S0550000000/github/doc/jawbreaker-fd0-145436.jpeg

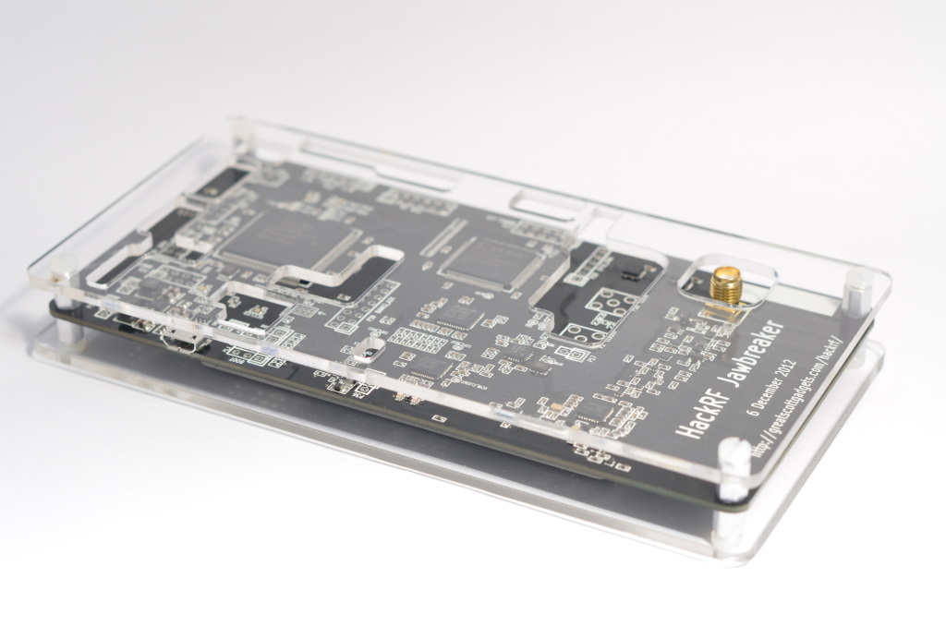
doc/jawbreaker-fd0-145436.jpeg
