S0550000000/github/doc/jawbreaker.jpeg

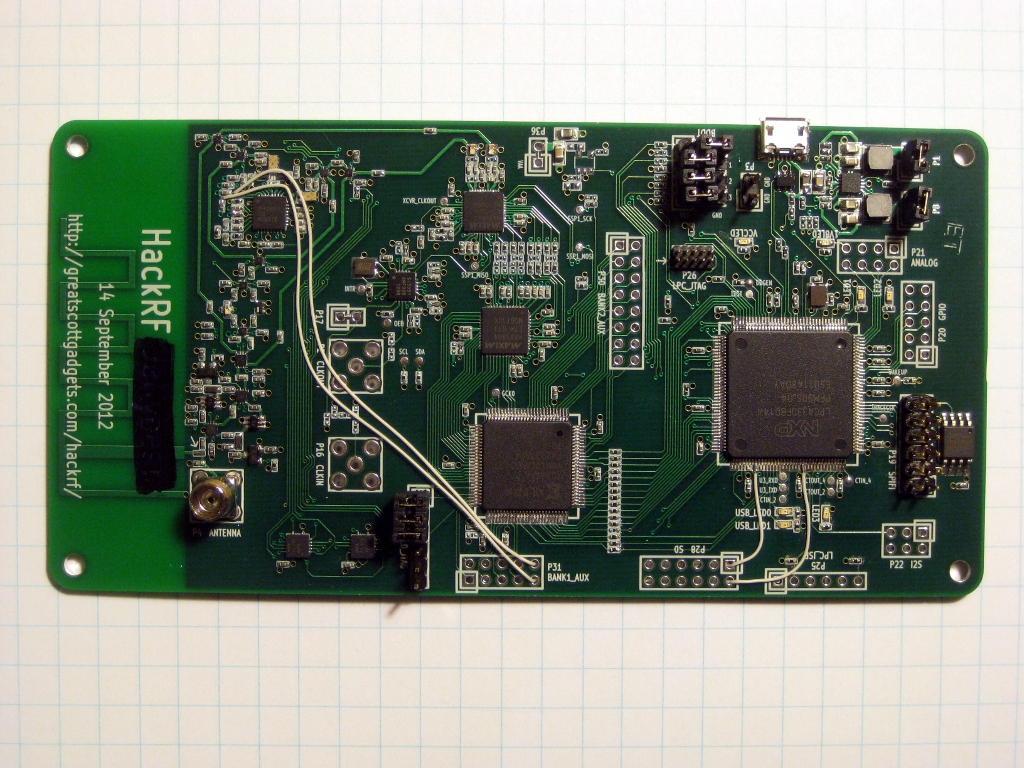
doc/jawbreaker.jpeg
