S0550000000/github/doc/lemonAndjelly.jpeg

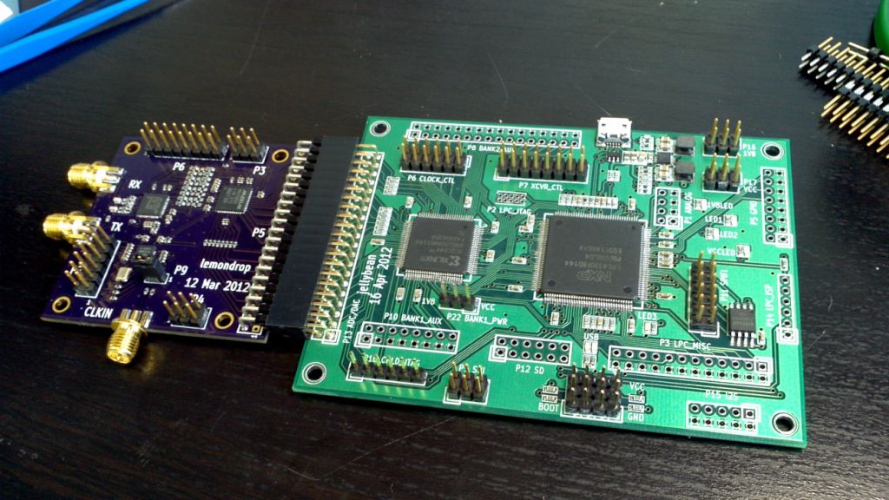
doc/lemonAndjelly.jpeg
