S0550000000/github/doc/wiki/images/hackrf_blockdiagram-digital.png

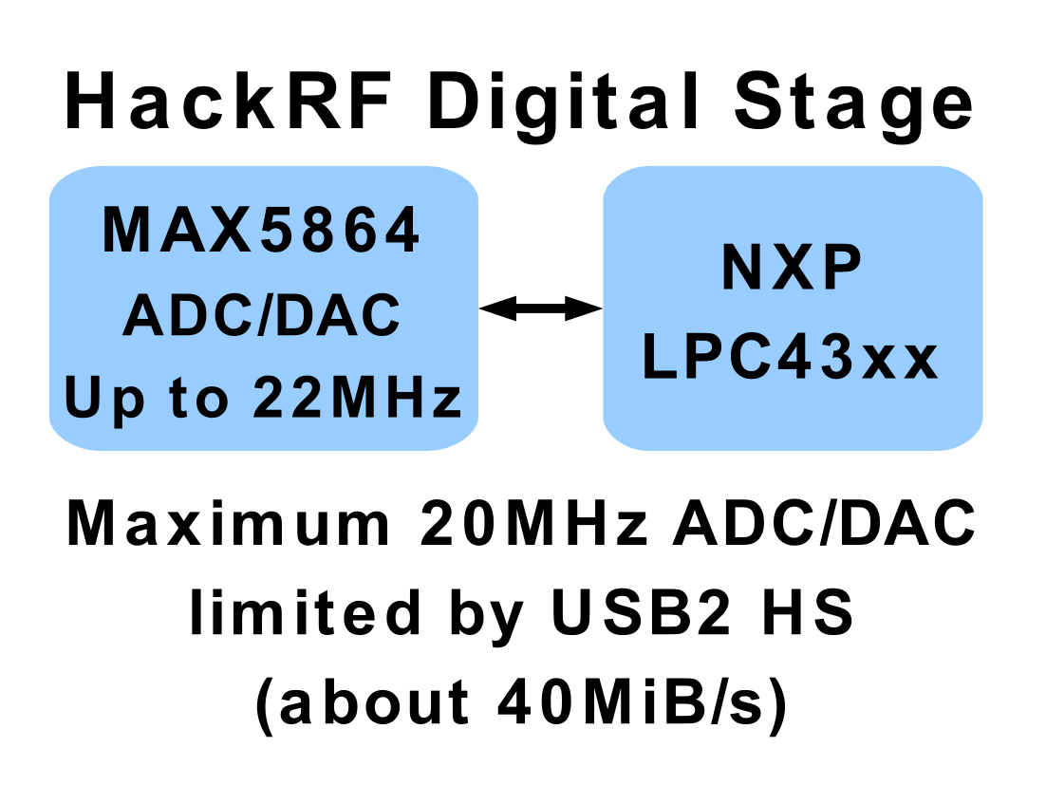
doc/wiki/images/hackrf_blockdiagram-digital.png
