S0550000000/github/doc/wiki/images/hackrf_blockdiagram-frontend_baseband.png

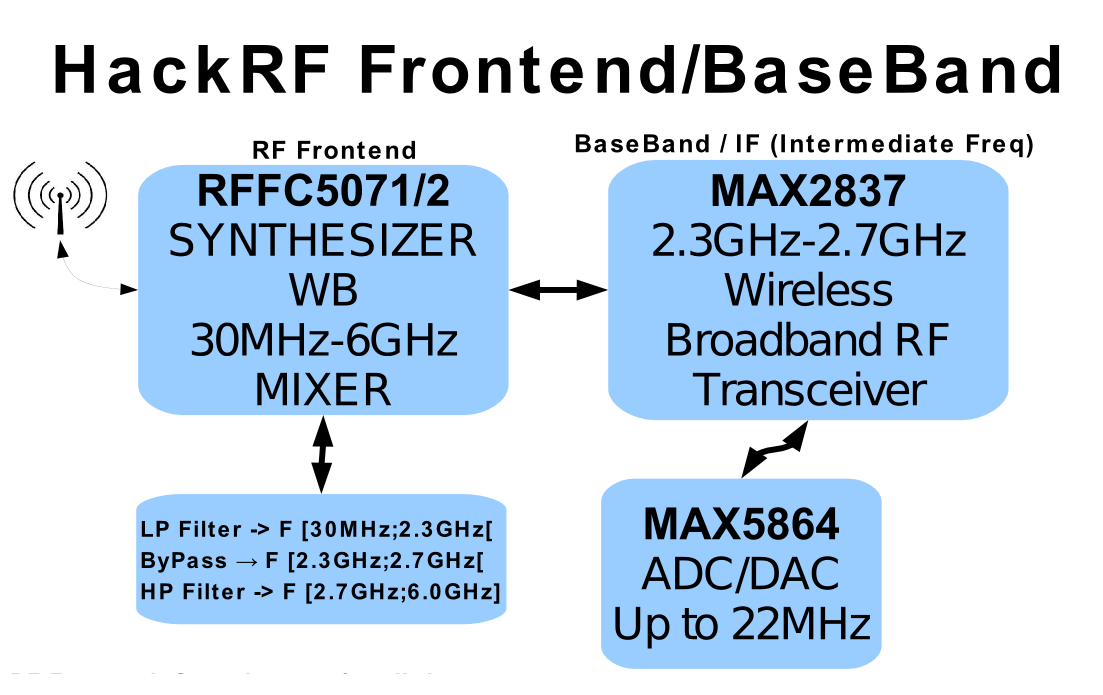
doc/wiki/images/hackrf_blockdiagram-frontend_baseband.png
