S0550000000/github/hardware/hackrf-one/PlasticCase_CAD/Case_With_HackRF.png

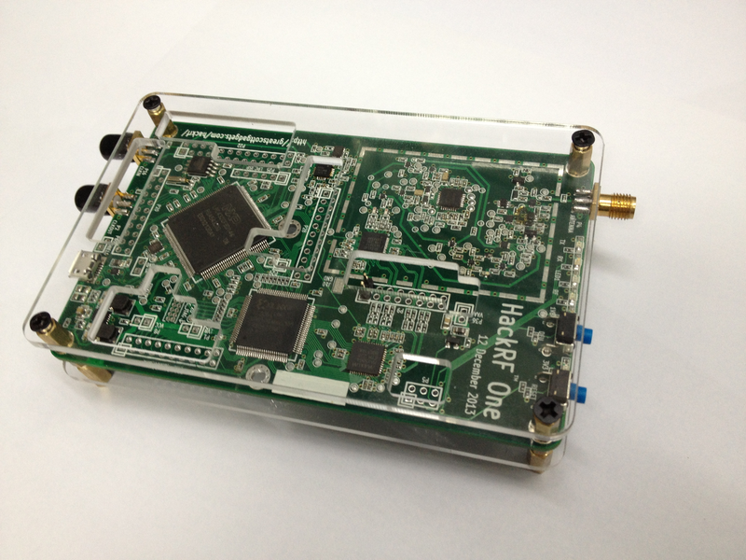
hardware/hackrf-one/PlasticCase_CAD/Case_With_HackRF.png
