S0550000000/github/hardware/hackrf-one/SoBv1_HackRF_One_16Janv2014/SoBv1_HackRF_One_Top2D.png

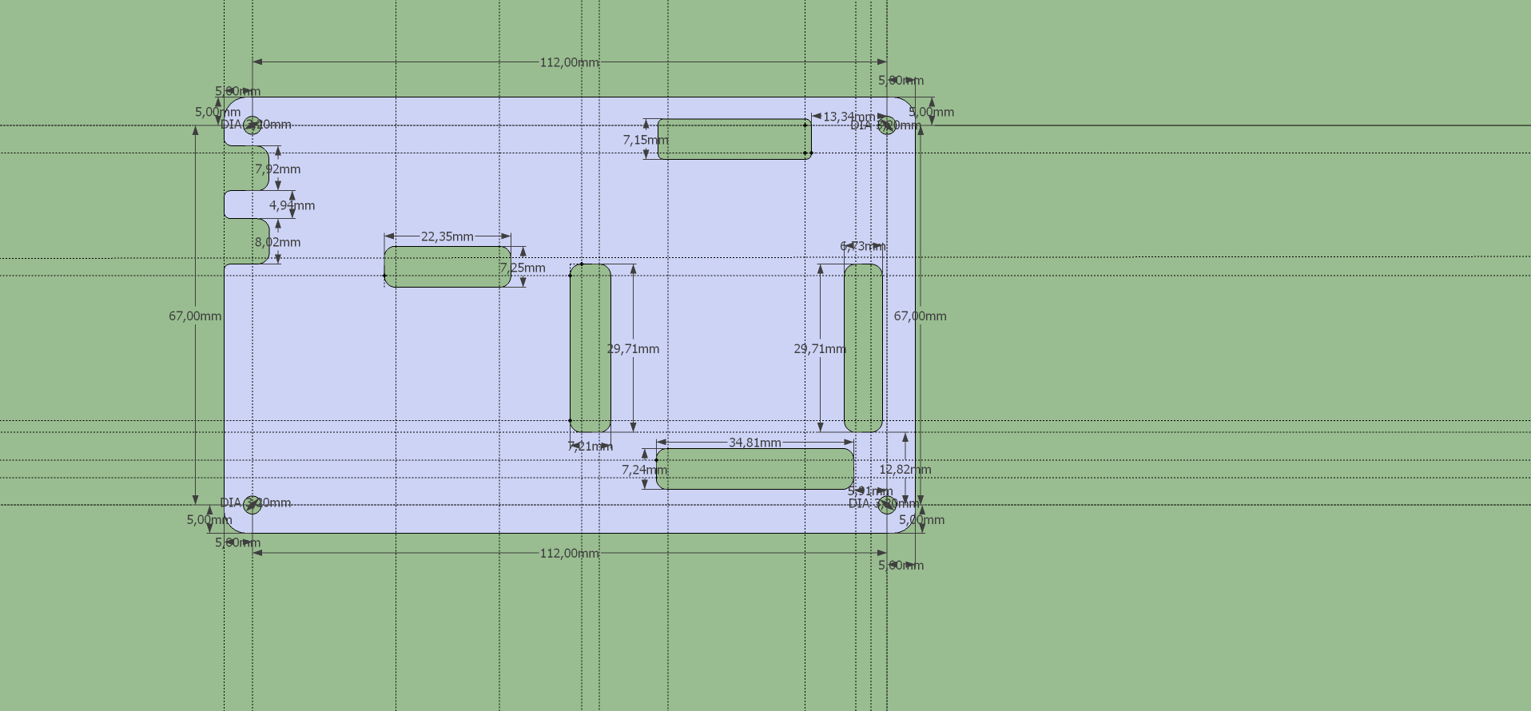
hardware/hackrf-one/SoBv1_HackRF_One_16Janv2014/SoBv1_HackRF_One_Top2D.png
