S0550000000/github/hardware/jellybean/JellyBean_pins.png

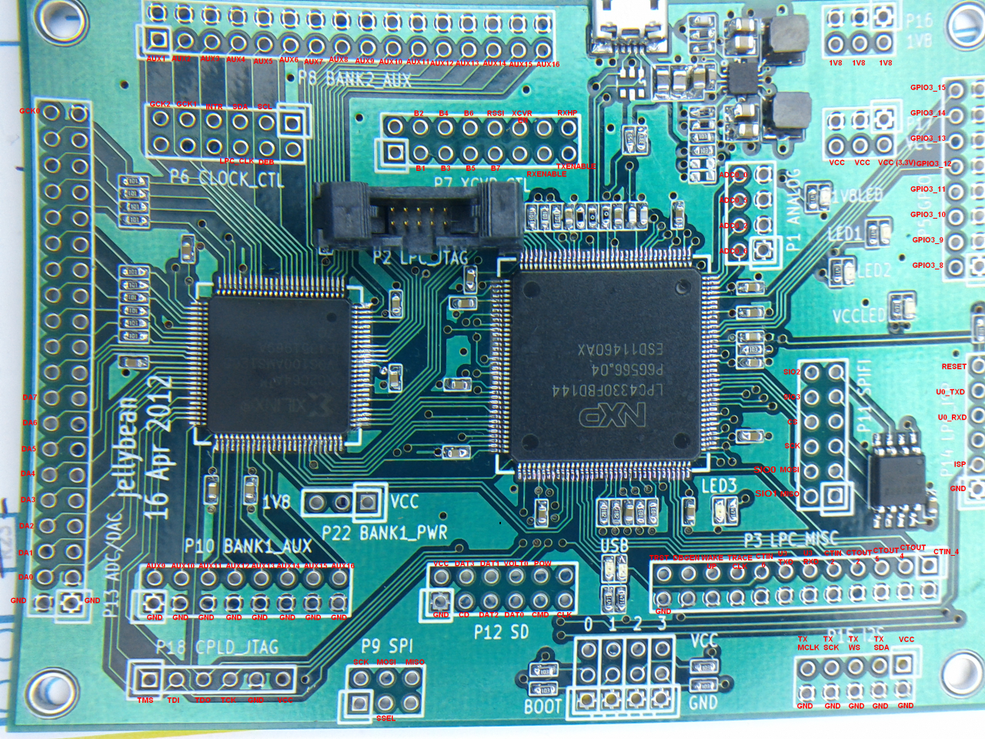
hardware/jellybean/JellyBean_pins.png
