S0550000000/github/firmware/common/tuning.c

/*
 * Copyright 2012 Jared Boone
 * Copyright 2013 Benjamin Vernoux
 *
 * This file is part of HackRF.
 *
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
 * You should have received a copy of the GNU General Public License
 * along with this program; see the file COPYING.  If not, write to
 * the Free Software Foundation, Inc., 51 Franklin Street,
 * Boston, MA 02110-1301, USA.
 */

#include "tuning.h"

#include "hackrf-ui.h"

#include <hackrf_core.h>
#include <mixer.h>
#include <max2837.h>
#include <sgpio.h>
#include <operacake.h>

#define FREQ_ONE_MHZ     (1000*1000)

#define MIN_LP_FREQ_MHZ (0)
#define MAX_LP_FREQ_MHZ (2150)

#define MIN_BYPASS_FREQ_MHZ (2150)
#define MAX_BYPASS_FREQ_MHZ (2750)

#define MIN_HP_FREQ_MHZ (2750)
#define MID1_HP_FREQ_MHZ (3600)
#define MID2_HP_FREQ_MHZ (5100)
#define MAX_HP_FREQ_MHZ (7250)

#define MIN_LO_FREQ_HZ (84375000)
#define MAX_LO_FREQ_HZ (5400000000ULL)

static uint32_t max2837_freq_nominal_hz=2560000000;

uint64_t freq_cache = 100000000;
/*
 * Set freq/tuning between 0MHz to 7250 MHz (less than 16bits really used)
 * hz between 0 to 999999 Hz (not checked)
 * return false on error or true if success.
 */
bool set_freq(const uint64_t freq)
{
	bool success;
	uint32_t mixer_freq_mhz;
	uint32_t MAX2837_freq_hz;
	uint64_t real_mixer_freq_hz;

	const uint32_t freq_mhz = freq / 1000000;
	const uint32_t freq_hz = freq % 1000000;

	success = true;

	const max2837_mode_t prior_max2837_mode = max2837_mode(&max2837);
	max2837_set_mode(&max2837, MAX2837_MODE_STANDBY);
	if(freq_mhz < MAX_LP_FREQ_MHZ)
	{
		rf_path_set_filter(&rf_path, RF_PATH_FILTER_LOW_PASS);
#ifdef RAD1O
		max2837_freq_nominal_hz = 2300000000;
#else
		/* IF is graduated from 2650 MHz to 2343 MHz */
		max2837_freq_nominal_hz = 2650000000 - (freq / 7);
#endif
		mixer_freq_mhz = (max2837_freq_nominal_hz / FREQ_ONE_MHZ) + freq_mhz;
		/* Set Freq and read real freq */
		real_mixer_freq_hz = mixer_set_frequency(&mixer, mixer_freq_mhz);
		max2837_set_frequency(&max2837, real_mixer_freq_hz - freq);
		sgpio_cpld_stream_rx_set_q_invert(&sgpio_config, 1);
	}else if( (freq_mhz >= MIN_BYPASS_FREQ_MHZ) && (freq_mhz < MAX_BYPASS_FREQ_MHZ) )
	{
		rf_path_set_filter(&rf_path, RF_PATH_FILTER_BYPASS);
		MAX2837_freq_hz = (freq_mhz * FREQ_ONE_MHZ) + freq_hz;
		/* mixer_freq_mhz <= not used in Bypass mode */
		max2837_set_frequency(&max2837, MAX2837_freq_hz);
		sgpio_cpld_stream_rx_set_q_invert(&sgpio_config, 0);
	}else if(  (freq_mhz >= MIN_HP_FREQ_MHZ) && (freq_mhz <= MAX_HP_FREQ_MHZ) )
	{
		if (freq_mhz < MID1_HP_FREQ_MHZ) {
			/* IF is graduated from 2150 MHz to 2750 MHz */
			max2837_freq_nominal_hz = 2150000000 + (((freq - 2750000000) * 60) / 85);
		} else if (freq_mhz < MID2_HP_FREQ_MHZ) {
			/* IF is graduated from 2350 MHz to 2650 MHz */
			max2837_freq_nominal_hz = 2350000000 + ((freq - 3600000000) / 5);
		} else {
			/* IF is graduated from 2500 MHz to 2738 MHz */
			max2837_freq_nominal_hz = 2500000000 + ((freq - 5100000000) / 9);
		}
		rf_path_set_filter(&rf_path, RF_PATH_FILTER_HIGH_PASS);
		mixer_freq_mhz = freq_mhz - (max2837_freq_nominal_hz / FREQ_ONE_MHZ);
		/* Set Freq and read real freq */
		real_mixer_freq_hz = mixer_set_frequency(&mixer, mixer_freq_mhz);
		max2837_set_frequency(&max2837, freq - real_mixer_freq_hz);
		sgpio_cpld_stream_rx_set_q_invert(&sgpio_config, 0);
	}else
	{
		/* Error freq_mhz too high */
		success = false;
	}
	max2837_set_mode(&max2837, prior_max2837_mode);
	if( success ) {
		freq_cache = freq;
		hackrf_ui()->set_frequency(freq);
#ifdef HACKRF_ONE
		operacake_set_range(freq_mhz);
#endif
	}
	return success;
}

bool set_freq_explicit(const uint64_t if_freq_hz, const uint64_t lo_freq_hz,
		const rf_path_filter_t path)
{
	if ((if_freq_hz < ((uint64_t)MIN_BYPASS_FREQ_MHZ * FREQ_ONE_MHZ))
			|| (if_freq_hz > ((uint64_t)MAX_BYPASS_FREQ_MHZ * FREQ_ONE_MHZ))) {
		return false;
	}

	if ((path != RF_PATH_FILTER_BYPASS) &&
			((lo_freq_hz < MIN_LO_FREQ_HZ) || (lo_freq_hz > MAX_LO_FREQ_HZ))) {
		return false;
	}

	if (path > 2) {
		return false;
	}

	rf_path_set_filter(&rf_path, path);
	max2837_set_frequency(&max2837, if_freq_hz);
	if (lo_freq_hz > if_freq_hz) {
		sgpio_cpld_stream_rx_set_q_invert(&sgpio_config, 1);
	} else {
		sgpio_cpld_stream_rx_set_q_invert(&sgpio_config, 0);
	}
	if (path != RF_PATH_FILTER_BYPASS) {
		(void)mixer_set_frequency(&mixer, lo_freq_hz / FREQ_ONE_MHZ);
	}
	return true;
}
