S0550000000/github/firmware/common/max2837.h

/*
 * Copyright 2012 Will Code? (TODO: Proper attribution)
 * Copyright 2014 Jared Boone <jared@sharebrained.com>
 *
 * This file is part of HackRF.
 *
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
 * You should have received a copy of the GNU General Public License
 * along with this program; see the file COPYING.  If not, write to
 * the Free Software Foundation, Inc., 51 Franklin Street,
 * Boston, MA 02110-1301, USA.
 */

#ifndef __MAX2837_H
#define __MAX2837_H

#include <stdint.h>
#include <stdbool.h>

#include "gpio.h"
#include "spi_bus.h"

/* 32 registers, each containing 10 bits of data. */
#define MAX2837_NUM_REGS 32
#define MAX2837_DATA_REGS_MAX_VALUE 1024

typedef enum {
	MAX2837_MODE_SHUTDOWN,
	MAX2837_MODE_STANDBY,
	MAX2837_MODE_TX,
	MAX2837_MODE_RX
} max2837_mode_t;

struct max2837_driver_t;
typedef struct max2837_driver_t max2837_driver_t;

struct max2837_driver_t {
	spi_bus_t* const bus;
	gpio_t gpio_enable;
	gpio_t gpio_rx_enable;
	gpio_t gpio_tx_enable;
	void (*target_init)(max2837_driver_t* const drv);
	void (*set_mode)(max2837_driver_t* const drv, const max2837_mode_t new_mode);
	max2837_mode_t mode;
	uint16_t regs[MAX2837_NUM_REGS];
	uint32_t regs_dirty;
};

/* Initialize chip. */
extern void max2837_setup(max2837_driver_t* const drv);

/* Read a register via SPI. Save a copy to memory and return
 * value. Mark clean. */
extern uint16_t max2837_reg_read(max2837_driver_t* const drv, uint8_t r);

/* Write value to register via SPI and save a copy to memory. Mark
 * clean. */
extern void max2837_reg_write(max2837_driver_t* const drv, uint8_t r, uint16_t v);

/* Write all dirty registers via SPI from memory. Mark all clean. Some
 * operations require registers to be written in a certain order. Use
 * provided routines for those operations. */
extern void max2837_regs_commit(max2837_driver_t* const drv);

max2837_mode_t max2837_mode(max2837_driver_t* const drv);
void max2837_set_mode(max2837_driver_t* const drv, const max2837_mode_t new_mode);

/* Turn on/off all chip functions. Does not control oscillator and CLKOUT */
extern void max2837_start(max2837_driver_t* const drv);
extern void max2837_stop(max2837_driver_t* const drv);

/* Set frequency in Hz. Frequency setting is a multi-step function
 * where order of register writes matters. */
extern void max2837_set_frequency(max2837_driver_t* const drv, uint32_t freq);
uint32_t max2837_set_lpf_bandwidth(max2837_driver_t* const drv, const uint32_t bandwidth_hz);
bool max2837_set_lna_gain(max2837_driver_t* const drv, const uint32_t gain_db);
bool max2837_set_vga_gain(max2837_driver_t* const drv, const uint32_t gain_db);
bool max2837_set_txvga_gain(max2837_driver_t* const drv, const uint32_t gain_db);
	
extern void max2837_tx(max2837_driver_t* const drv);
extern void max2837_rx(max2837_driver_t* const drv);

#endif // __MAX2837_H
